KevLe12/Vamora75/Artwork/Vamora75_name_black.png

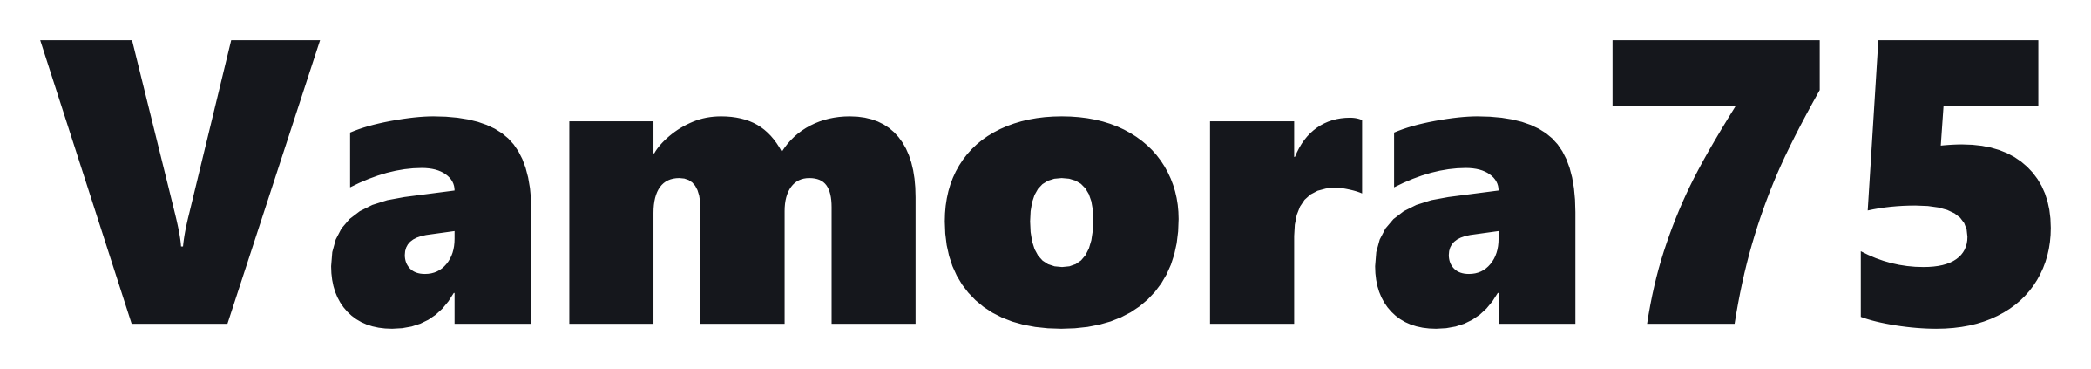
Artwork/Vamora75_name_black.png
