KevLe12/Vamora75/Artwork/Vamora75_name_on_graphite.png

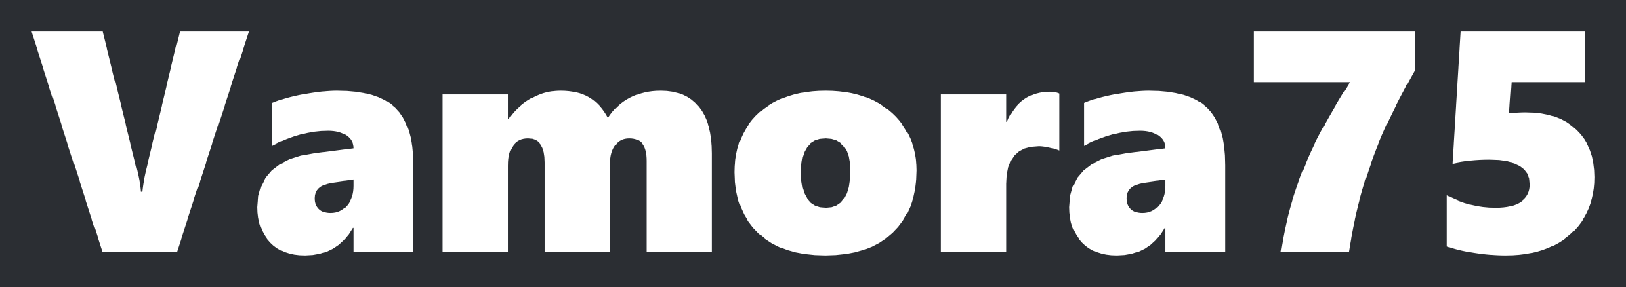
Artwork/Vamora75_name_on_graphite.png
