KevLe12/Vamora75/PCB/3dmodels/R_0402_1005Metric.step

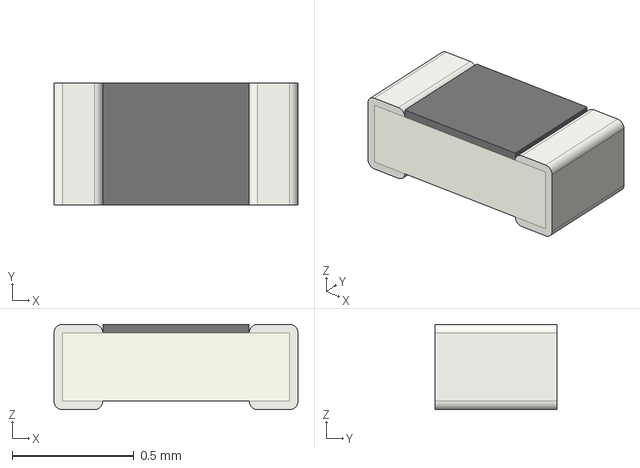
[picture p29: CAD file, 2026-10-02]
PCB/3dmodels/R_0402_1005Metric.step
1.00 x 0.5 x 0.35 mm
