KevLe12/Vamora75/PCB/3dmodels/Winbond_USON-8-1EP_3x2mm_P0.5mm_EP0.2x1.6mm.step

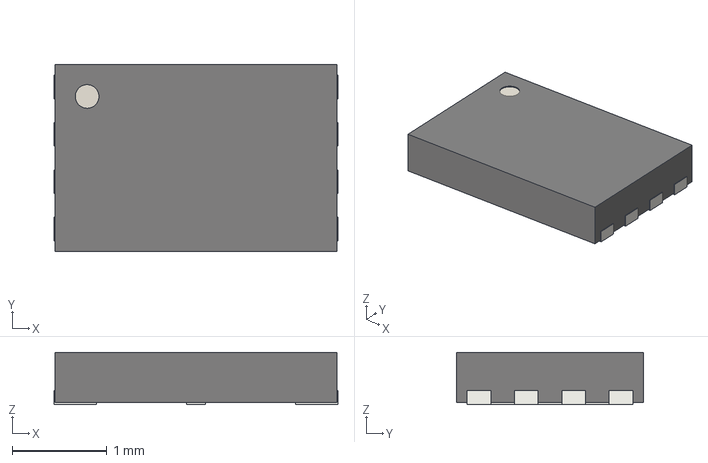
[picture p30: CAD file, 2026-10-02]
PCB/3dmodels/Winbond_USON-8-1EP_3x2mm_P0.5mm_EP0.2x1.6mm.step
3.00 x 1.98 x 0.55 mm
