KevLe12/Vamora75/PCB/3dmodels/Stabilizer_MX_2.00u.step

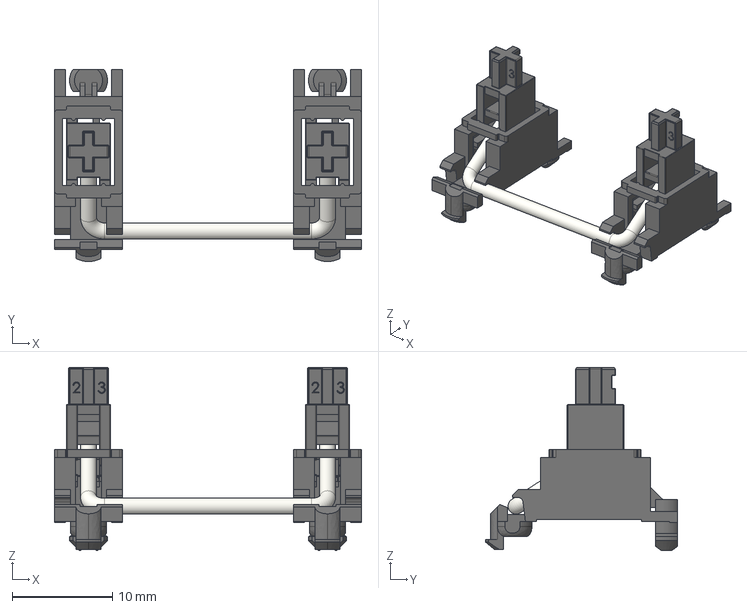
[picture p31: CAD file, 2026-10-02]
PCB/3dmodels/Stabilizer_MX_2.00u.step
30.7 x 19.2 x 18.3 mm
