KevLe12/Vamora75/PCB/3dmodels/QFN-56-1EP_7x7mm_P0.4mm_EP3.2x3.2mm.step

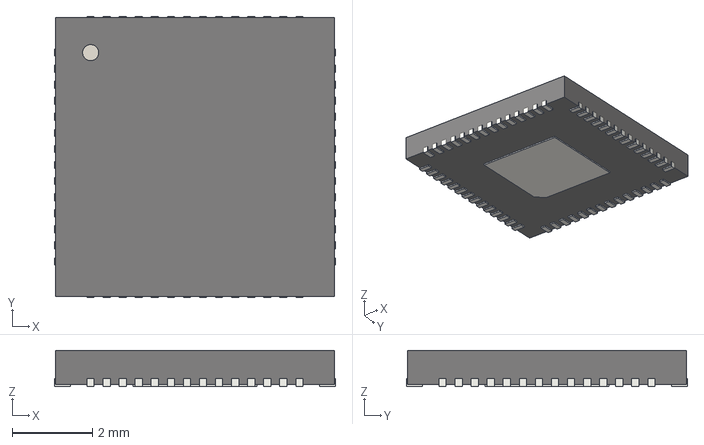
[picture p32: CAD file, 2026-10-02]
PCB/3dmodels/QFN-56-1EP_7x7mm_P0.4mm_EP3.2x3.2mm.step
7.00 x 7.00 x 0.9 mm
