KevLe12/Vamora75/PCB/3dmodels/Fuse_0805_2012Metric.step

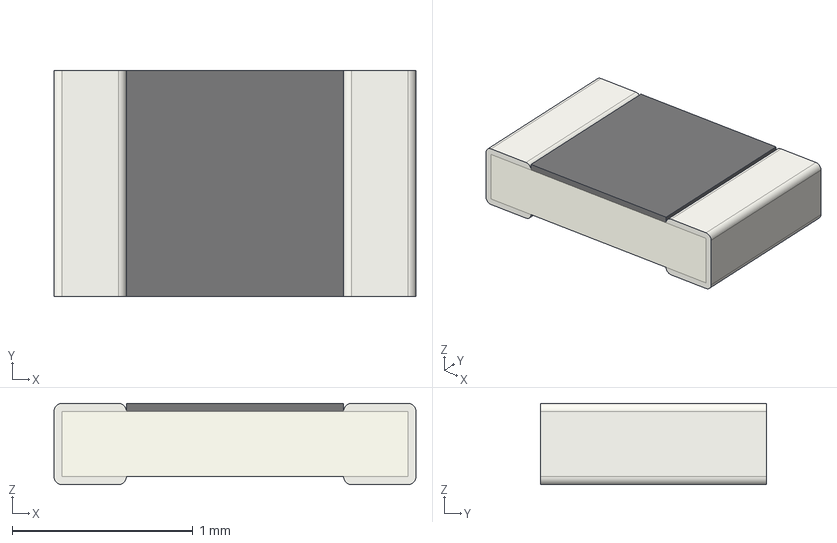
[picture p33: CAD file, 2026-10-02]
PCB/3dmodels/Fuse_0805_2012Metric.step
2.00 x 1.25 x 0.45 mm
