KevLe12/Vamora75/PCB/3dmodels/MX_PCB.step

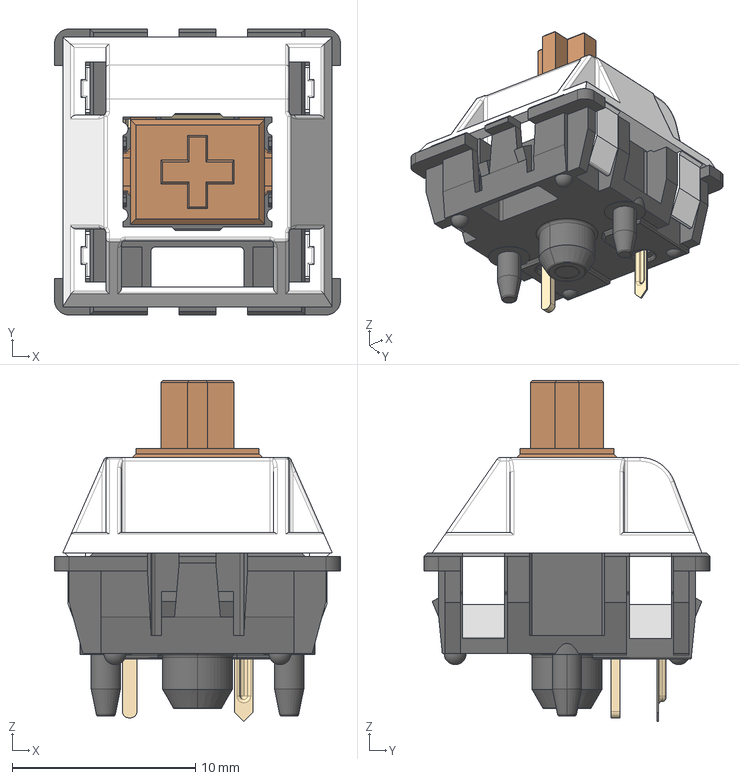
[picture p34: CAD file, 2026-10-02]
PCB/3dmodels/MX_PCB.step
15.6 x 15.6 x 18.6 mm
