KevLe12/Vamora75/PCB/3dmodels/Hotswap_MX.step

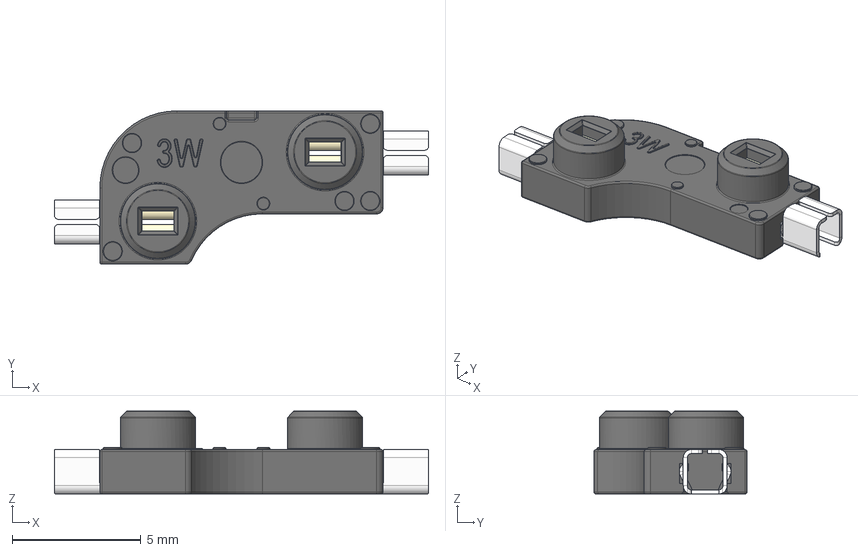
[picture p35: CAD file, 2026-10-02]
PCB/3dmodels/Hotswap_MX.step
14.5 x 5.95 x 3.22 mm
