KevLe12/Vamora75/PCB/3dmodels/SOT-23.step

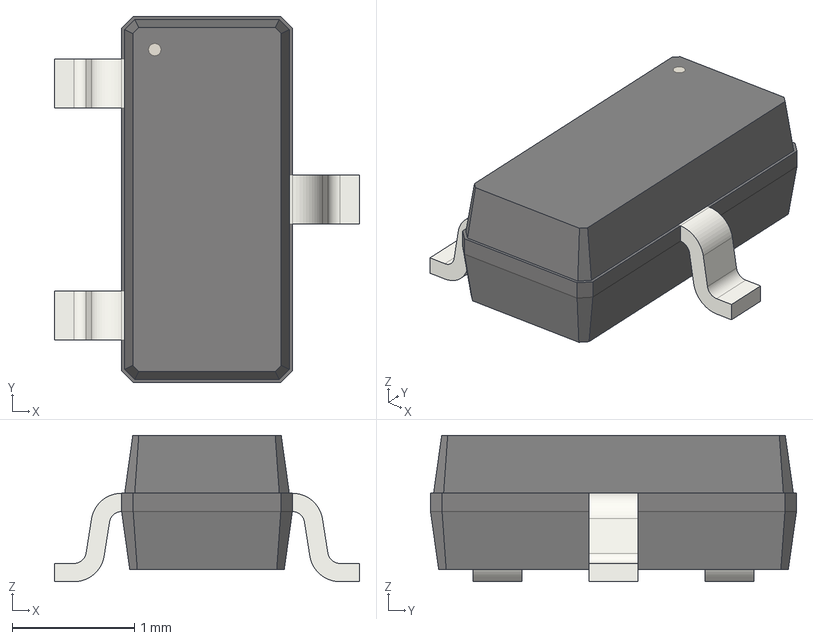
[picture p36: CAD file, 2026-10-02]
PCB/3dmodels/SOT-23.step
2.50 x 3.00 x 1.20 mm
