KevLe12/Vamora75/PCB/3dmodels/SOT-23-6.step

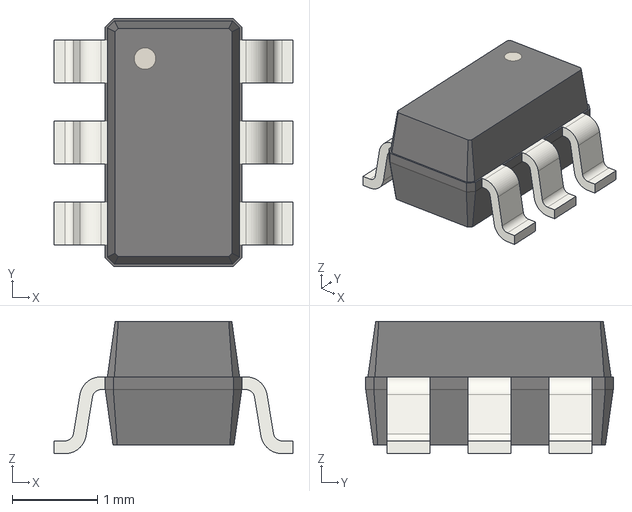
[picture p37: CAD file, 2026-10-02]
PCB/3dmodels/SOT-23-6.step
2.80 x 2.90 x 1.55 mm
