KevLe12/Vamora75/PCB/3dmodels/Crystal_SMD_3225-4Pin_3.2x2.5mm.step

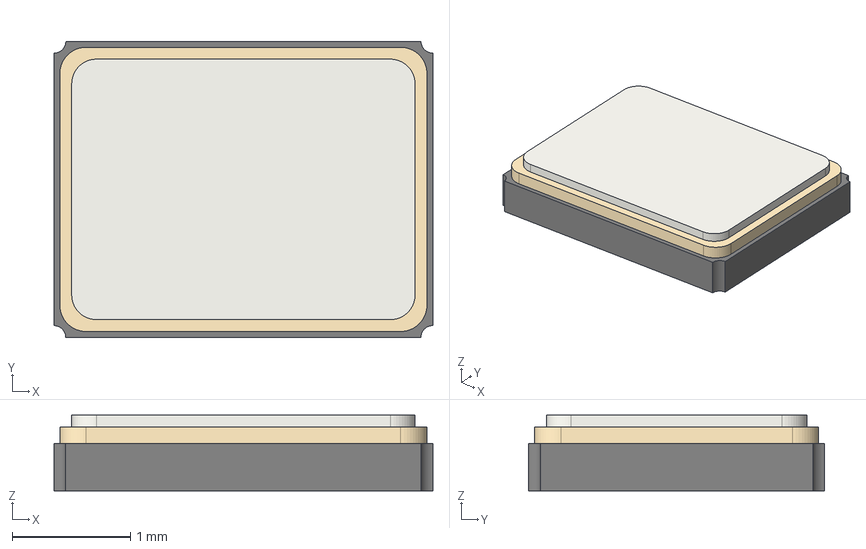
[picture p38: CAD file, 2026-10-02]
PCB/3dmodels/Crystal_SMD_3225-4Pin_3.2x2.5mm.step
3.20 x 2.50 x 0.64 mm
