KevLe12/Vamora75/PCB/3dmodels/USB_C_HRO_TYPE-C-31-M-12.step

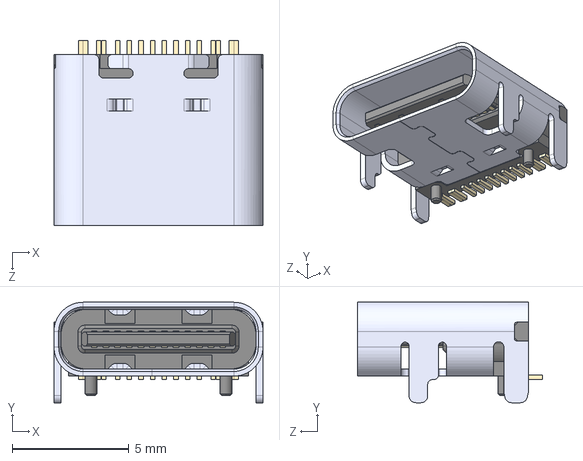
[picture p39: CAD file, 2026-10-02]
PCB/3dmodels/USB_C_HRO_TYPE-C-31-M-12.step
8.94 x 4.30 x 7.90 mm
