KevLe12/Vamora75/PCB/3dmodels/Diode_SOD-123.step

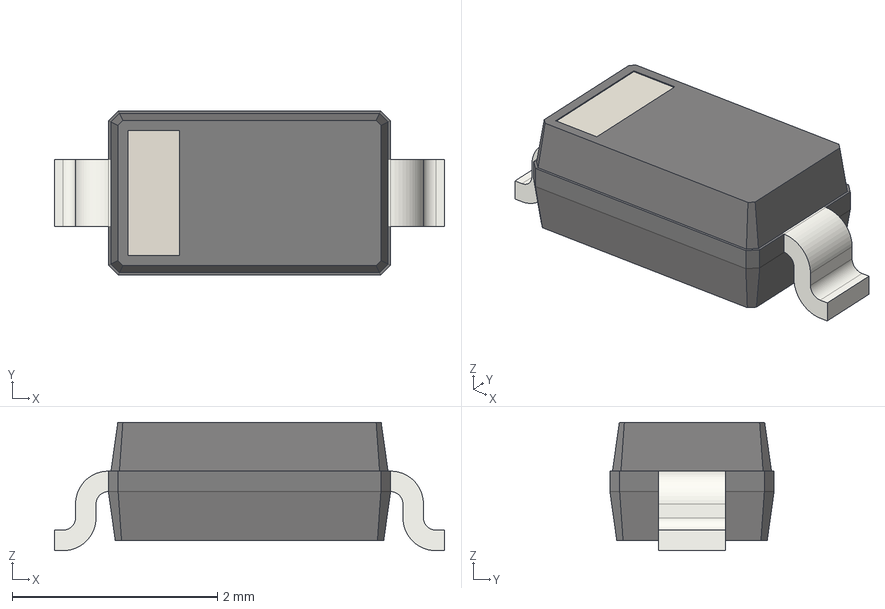
[picture p40: CAD file, 2026-10-02]
PCB/3dmodels/Diode_SOD-123.step
3.80 x 1.60 x 1.25 mm
