KevLe12/Vamora75/PCB/3dmodels/Stabilizer_MX_6.25u.step

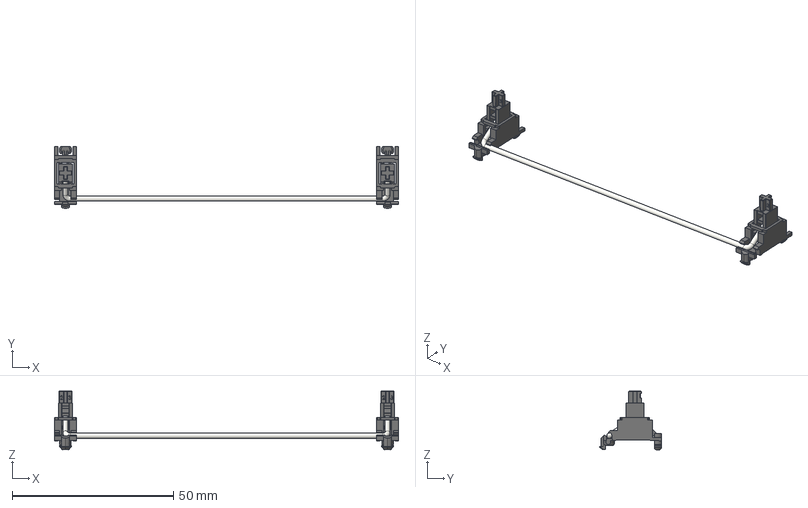
[picture p41: CAD file, 2026-10-02]
PCB/3dmodels/Stabilizer_MX_6.25u.step
106.8 x 19.2 x 18.3 mm
